NaohiroIIDA/custom-l-connector-guide/images/s-IMG_9315.jpg

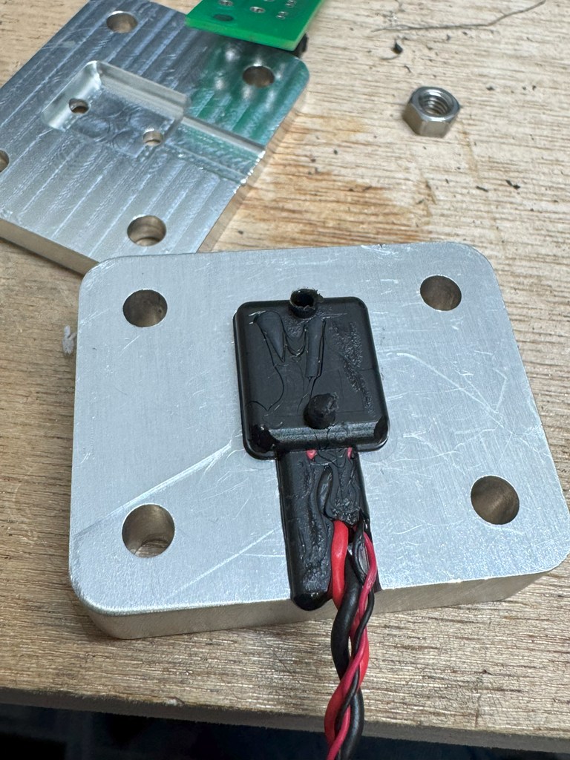
images/s-IMG_9315.jpg
