NaohiroIIDA/custom-l-connector-guide/images/JLCCNC_Order.png

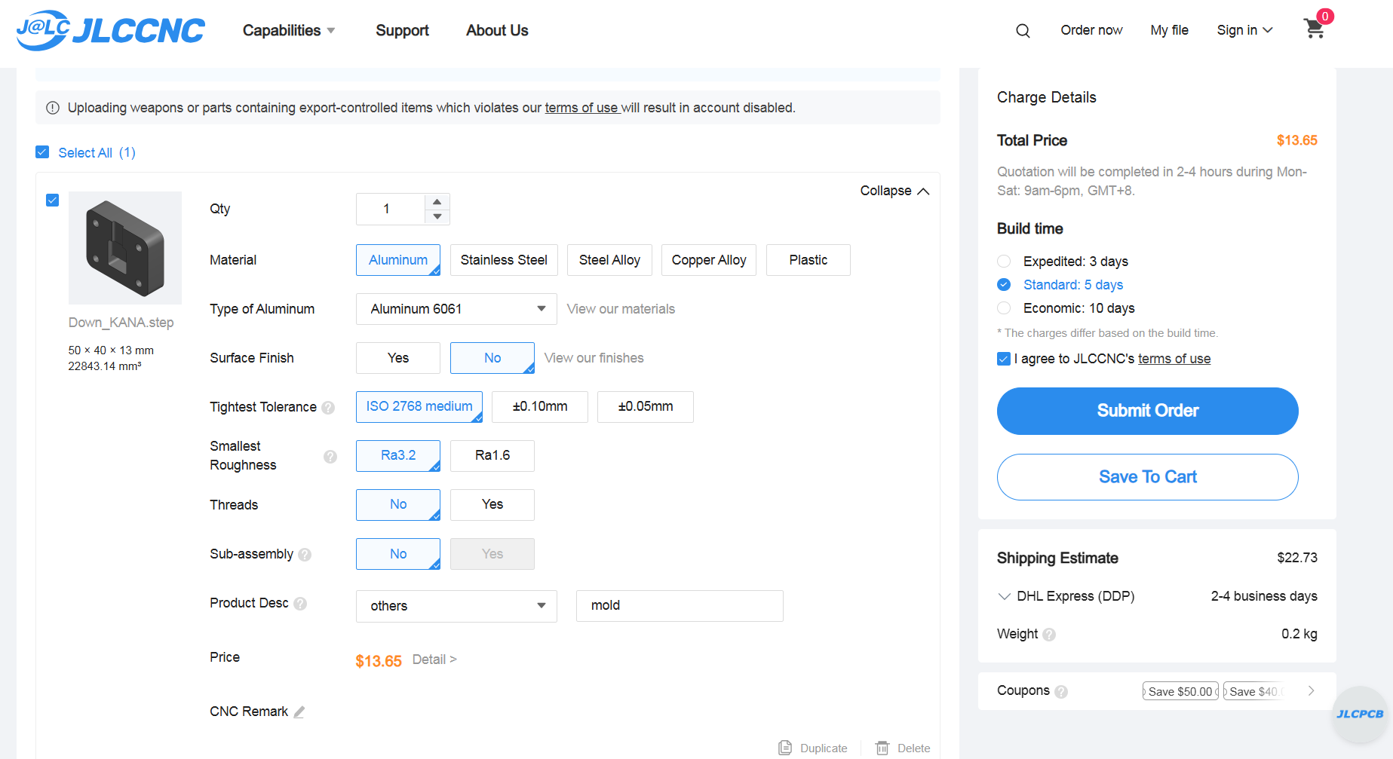
images/JLCCNC_Order.png
